pggood/ArduinoJimStim/Arduino_JimStim/wheels_default.h

const uint8_t WHEEL[] PROGMEM = {
//wheel0
// this is  dizzy, EDIS, whatever like old stim
//format of wheel pattern is
//output byte, delay factor (angular or time)
00,00,  //Fudge for the start
00,45,
01,45,   //1
00,45,
01,45,   //1
00,45,
01,45,   //1
00,45,
01,45,   //1
0xff,0,

//wheel1
// this is 36-1 with 2nd trigger pulse
//format of wheel pattern is
//output byte, delay factor (angular or time)
00,5,
01,5,   //1
00,5,
01,5,   //2
00,5,
01,5,   //3
00,5,
01,5,   //4
00,5,
01,5,   //5
00,5,
01,5,   //6
00,5,
01,5,   //7
00,5,
01,5,   //8
00,5,
01,5,   //9
00,5,
01,5,   //10
00,5,
01,5,   //11
00,5,
01,5,   //12
00,5,
01,5,   //13
00,5,
01,5,   //14
00,5,
01,5,   //15
00,5,
01,5,   //16
00,5,
01,5,   //17
00,5,
01,5,   //18
00,5,
01,5,   //19
00,5,
01,5,   //20
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
03,5,   //33 // 2nd
02,5,				// trig
03,5,   //34 // in
02,5,				// here
01,5,   //35
00,5,
00,5,   //36 (missing tooth)
00,5,
01,5,   //1   // 2nd rev
00,5,
01,5,   //2
00,5,
01,5,   //3
00,5,
01,5,   //4
00,5,
01,5,   //5
00,5,
01,5,   //6
00,5,
01,5,   //7
00,5,
01,5,   //8
00,5,
01,5,   //9
00,5,
01,5,   //10
00,5,
01,5,   //11
00,5,
01,5,   //12
00,5,
01,5,   //13
00,5,
01,5,   //14
00,5,
01,5,   //15
00,5,
01,5,   //16
00,5,
01,5,   //17
00,5,
01,5,   //18
00,5,
01,5,   //19
00,5,
01,5,   //20
00,5,
01,5,   //21
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
00,5,   //36 (missing tooth)
0xff,0,    // terminating string

//wheel2
// 60-2 with 2nd trigger during missing teeth on 2nd rev
//format of wheel pattern is
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
00,5,
01,5,   //23
00,5,
01,5,   //24
00,5,
01,5,   //25
00,5,
03,5,   //26
02,5,
01,5,   //27
00,5,
03,5,   //28
02,5,
01,5,   //29
00,5,
03,5,   //30
02,5,
01,5,   //31
00,5,
01,5,   //32
00,5,
01,5,   //33
00,5,
01,5,   //34
00,5,
03,5,   //35
02,5,
01,5,   //36 
0xff};  // terminating string
